makingdevices/PixelBytes/Validation/Display/screen1.jpg

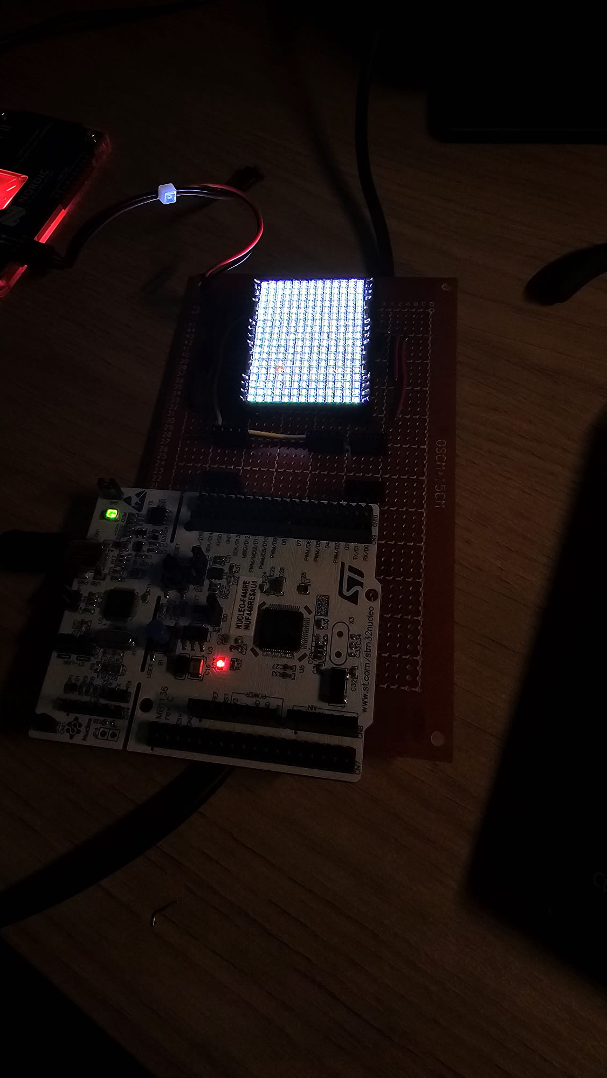
Validation/Display/screen1.jpg
