makingdevices/PixelBytes/Validation/Display/screen2.jpg

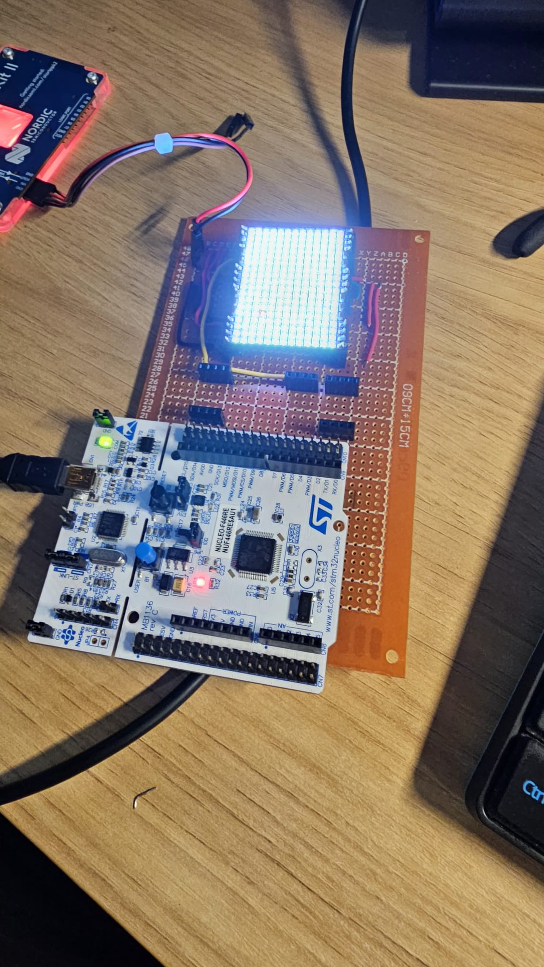
Validation/Display/screen2.jpg
