makingdevices/PixelBytes/Firmware/STM32F103_demo/ArduinoPlatform.cpp

/**
 ***************************************************************************************************
 * This file is part of WE Sensors SDK:
 * https://www.we-online.com/sensors
 *
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
 * THIS SOURCE CODE IS PROTECTED BY A LICENSE.
 * FOR MORE INFORMATION PLEASE CAREFULLY READ THE LICENSE AGREEMENT FILE LOCATED
 * IN THE ROOT DIRECTORY OF THIS DRIVER PACKAGE.
 *
 * COPYRIGHT (c) 2019 Würth Elektronik eiSos GmbH & Co. KG
 *
 ***************************************************************************************************
 **/

#include "ArduinoPlatform.h"
#include <Wire.h>

int deviceAddress = 0;

/**
 * @brief  Initialize the I2C Interface
 * @param  I2C address
 * @retval Error Code
 */

int I2CInit(int address)
{
	uint32_t timeout = (uint32_t)(TIMEOUT_MS * 1000);  /* timeout in us */
	bool reset_on_timeout = false;
	
    deviceAddress = address;
    Wire.begin();
	
    return WE_SUCCESS;
}


int I2CDeInit(void)
{
    Wire.endTransmission(true);	/* end i2c transmission with stop = true, releasing the interface */
    return WE_SUCCESS;
}

/**
 * @brief  Set I2C bus Address
 * @param  I2C address
 * @retval Set Address
 */

void I2CSetAddress(int address) 
{ 
	deviceAddress = address; 
}

/**
 * @brief   Read data starting from the addressed register
 * @param  -RegAdr : register address to read from
 *         -NumByteToRead : number of bytes to read
 *         -pointer Data : address stores the data
 * @retval Error Code
 */

int ReadReg(uint8_t RegAdr, int NumByteToRead, uint8_t *Data)
{
	if (0 == NumByteToRead)
	{
		return WE_FAIL;
	}

    Wire.beginTransmission(deviceAddress);
    Wire.write(RegAdr);
	Wire.endTransmission();
	
    int n = Wire.requestFrom(deviceAddress, NumByteToRead);	
	if (n != NumByteToRead) /* also includes: if n == 0 */
	{
		return WE_FAIL;
	}
	
    for (int i = 0; i < n; i++)
    {
        Data[i] = Wire.read();
    }

    return WE_SUCCESS;
}

/**
 * @brief  Write data starting from the addressed register
 * @param  -RegAdr : address to write in
 *         -NumByteToWrite : number of bytes to write
 *         -pointer Data : address of the data to be written
 * @retval Error Code
 */

int WriteReg(uint8_t RegAdr, int NumByteToWrite, uint8_t *Data)
{

	if (0 == NumByteToWrite)
	{
		return WE_FAIL;
	}

    Wire.beginTransmission(deviceAddress);
    Wire.write(RegAdr);
	
	for (int i = 0; i < NumByteToWrite; i++)
    {
        Wire.write(Data[i]);
    }
	
	if (Wire.endTransmission()) /* slave ack or nack */
    {
        return WE_FAIL;
    }

    return WE_SUCCESS;
}

 /**
 * @brief   Read data starting from the addressed register
 * @param  -pointer Data : the address store the data
 *         -NumByteToRead : number of bytes to read     
 * @retval Error Code
 */

int I2C_read(uint8_t *data, int bytesToRead)
{
	Wire.beginTransmission(deviceAddress);
    int n = Wire.requestFrom(deviceAddress, bytesToRead); // request Bytes
	
	if (n != bytesToRead) /* also includes: if n == 0 */
	{
		return WE_FAIL;
	}	

	for(int index = 0; index < bytesToRead; index++)
	{
		data[index] = Wire.read();
	}
    
    return WE_SUCCESS;
}
/**         EOF         */
